retro-city/ks-330-mini/img/diamond-series.jpg

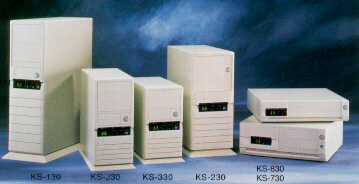
img/diamond-series.jpg
