retro-city/ks-330-mini/img/ks-330-mini-beta1.jpg

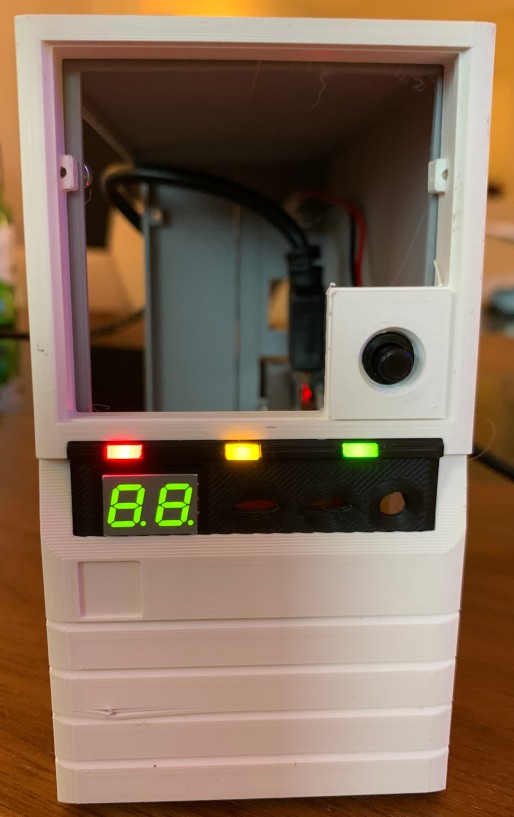
img/ks-330-mini-beta1.jpg
