retro-city/ks-330-mini/stl/mini/1.0-beta2/ks-330-mini-front-1.0-beta2.stl

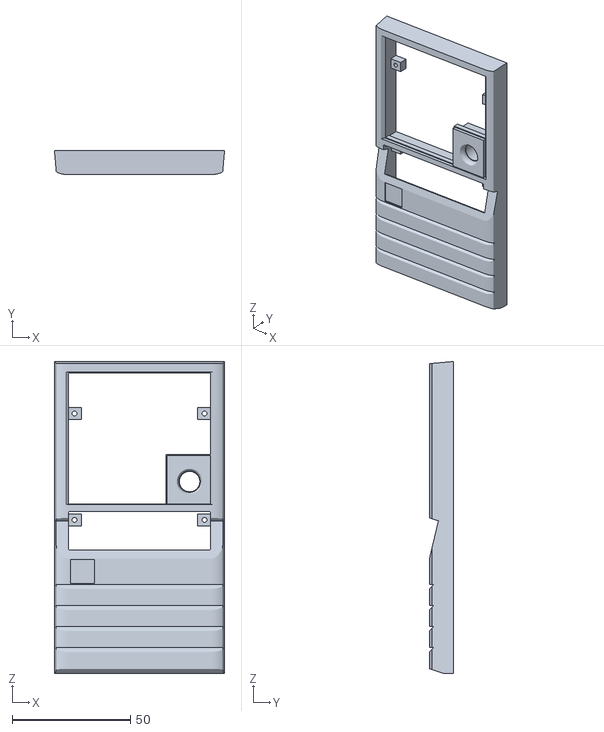
[picture p35: CAD file, 2020-07-30]
stl/mini/1.0-beta2/ks-330-mini-front-1.0-beta2.stl
72.0 x 10.2 x 132.0
