retro-city/ks-330-mini/stl/mini/1.0-beta3/ks-330-mini-frame-right-rpi-1.0-beta3.stl

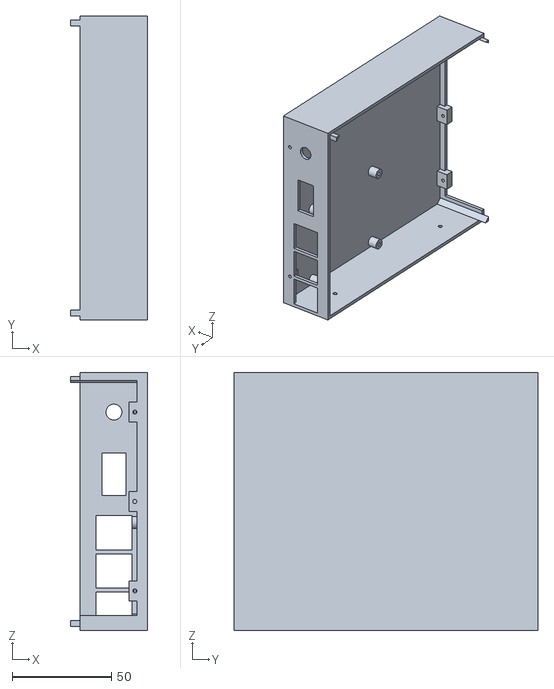
[picture p36: CAD file, 2020-08-06]
stl/mini/1.0-beta3/ks-330-mini-frame-right-rpi-1.0-beta3.stl
39.0 x 153.0 x 130.0
