retro-city/ks-330-mini/stl/mini/1.0-beta2/ks-330-mini-io-panel-1.0-beta2.stl

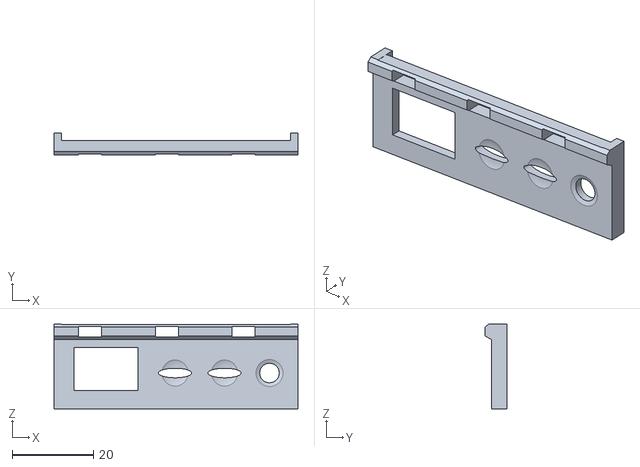
[picture p37: CAD file, 2020-07-30]
stl/mini/1.0-beta2/ks-330-mini-io-panel-1.0-beta2.stl
59.9 x 5.44 x 20.8
