retro-city/ks-330-mini/stl/mini/1.0-beta3/ks-330-mini-drive-bay-plain-1.0-beta3.stl

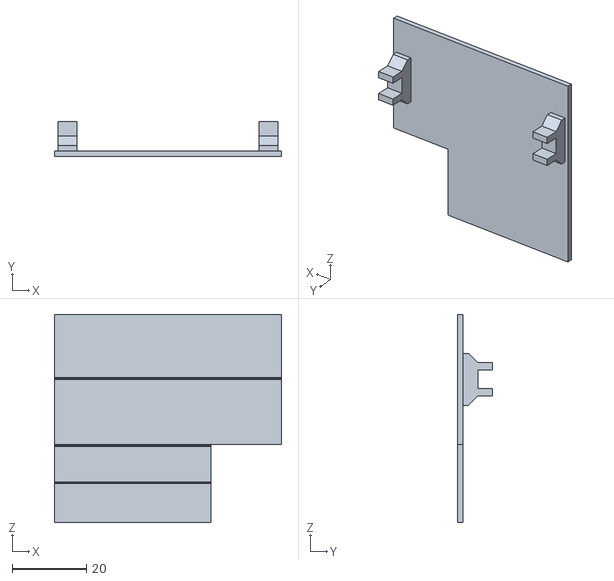
[picture p39: CAD file, 2020-08-06]
stl/mini/1.0-beta3/ks-330-mini-drive-bay-plain-1.0-beta3.stl
61.0 x 9.50 x 56.0
